matthiasnowak/jewelled/res/jewelled_chargerProgrammer_pcb_combined.png

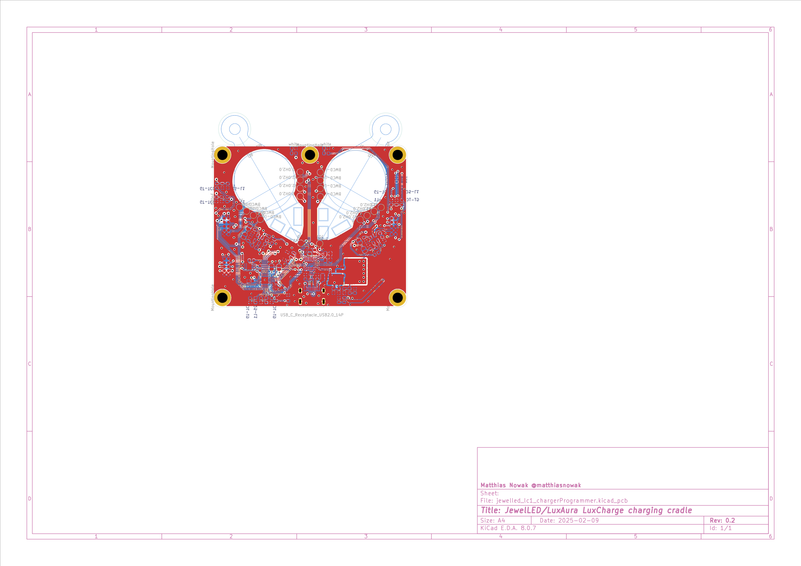
res/jewelled_chargerProgrammer_pcb_combined.png
