matthiasnowak/jewelled/res/jewelled_chargerProgrammer_render_back.png

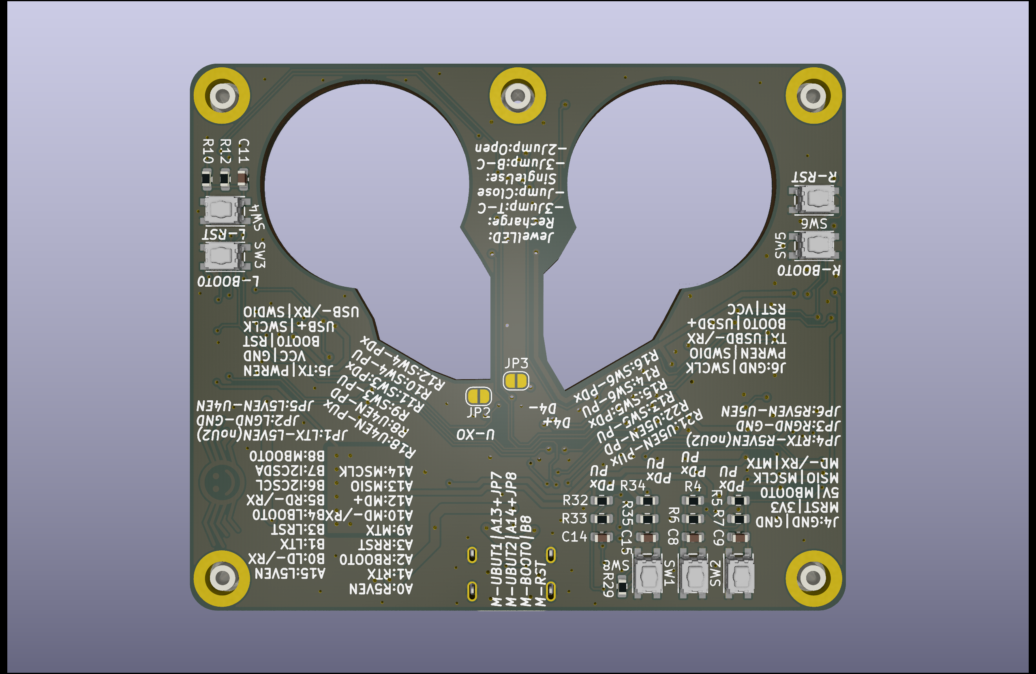
res/jewelled_chargerProgrammer_render_back.png
