matthiasnowak/jewelled/res/jewelled_dual_pcb_combined.png

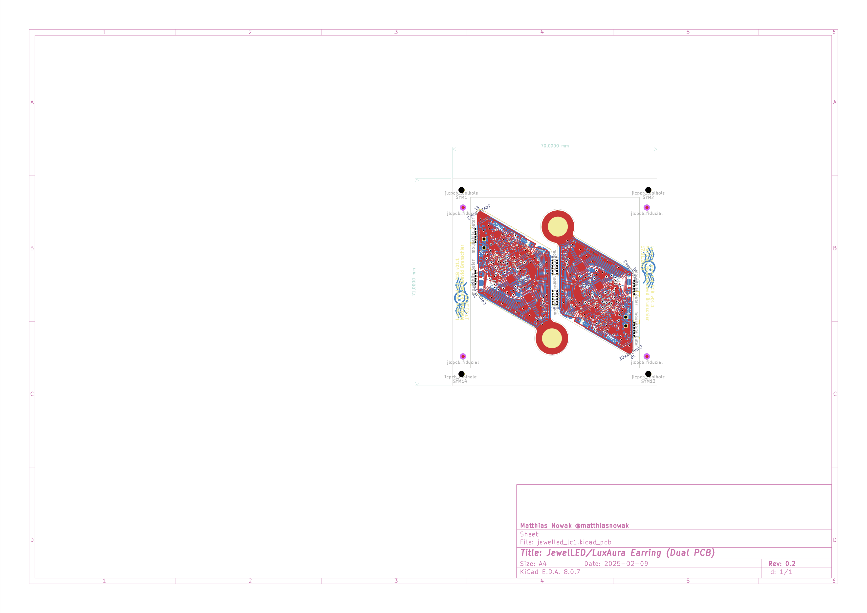
res/jewelled_dual_pcb_combined.png
