matthiasnowak/jewelled/software/CH32V203G6U6_jewelled_march/User/jewel_gpio.c

/*
 * jewel_gpio.c
 *
 *  Created on: 3 Mar 2025
 *      Author: matth
 */

#include "jewel_gpio.h"

void GPIO_Init_Config(void) {
    RCC_APB2PeriphClockCmd(RCC_APB2Periph_GPIOA, ENABLE);
    RCC_APB2PeriphClockCmd(RCC_APB2Periph_GPIOB, ENABLE);
    GPIO_InitTypeDef GPIO_InitStructure = {0};

    // GPIOB_0:     OPA1_P
    GPIO_InitStructure.GPIO_Pin = IO_OPA_P_PIN;
    GPIO_InitStructure.GPIO_Mode = GPIO_Mode_IN_FLOATING;
    GPIO_InitStructure.GPIO_Speed = GPIO_Speed_10MHz;
    GPIO_Init(IO_OPA_P_PORT, &GPIO_InitStructure);

    // GPIOA_6:     OPA1_N
    GPIO_InitStructure.GPIO_Pin = IO_OPA_N_PIN;
    GPIO_InitStructure.GPIO_Mode = GPIO_Mode_IN_FLOATING;
    GPIO_InitStructure.GPIO_Speed = GPIO_Speed_10MHz;
    GPIO_Init(IO_OPA_N_PORT, &GPIO_InitStructure);

    // GPIOB_1:     Dont init OPA1_OUT1 as GPIO
//    GPIO_InitStructure.GPIO_Pin = IO_OPA_O_PIN;
//    GPIO_InitStructure.GPIO_Mode = GPIO_Mode_AIN;
//    GPIO_InitStructure.GPIO_Speed = GPIO_Speed_10MHz;
//    GPIO_Init(IO_OPA_O_PORT, &GPIO_InitStructure);

    // GPIOA_5:     MICOUT
    GPIO_InitStructure.GPIO_Pin = IO_MICOUT_PIN;
    GPIO_InitStructure.GPIO_Mode = GPIO_Mode_AIN;
    GPIO_InitStructure.GPIO_Speed = GPIO_Speed_10MHz;
    GPIO_Init(IO_MICOUT_PORT, &GPIO_InitStructure);

    // GPIOA_0:     BUT1
    GPIO_InitStructure.GPIO_Pin = GPIO_Pin_0;
    GPIO_InitStructure.GPIO_Mode = GPIO_Mode_IPU;
    GPIO_InitStructure.GPIO_Speed = GPIO_Speed_50MHz;
    GPIO_Init(GPIOA, &GPIO_InitStructure);

    // GPIOA_1:     BUT2
    GPIO_InitStructure.GPIO_Pin = GPIO_Pin_1;
    GPIO_InitStructure.GPIO_Mode = GPIO_Mode_IPU;
    GPIO_InitStructure.GPIO_Speed = GPIO_Speed_50MHz;
    GPIO_Init(IO_BUT2_PORT, &GPIO_InitStructure);

    // GPIOA_2:     BUZZER
    GPIO_StructInit(&GPIO_InitStructure);
    GPIO_InitStructure.GPIO_Pin = IO_BUZZ_PIN;
    GPIO_InitStructure.GPIO_Mode = GPIO_Mode_Out_PP;
    GPIO_InitStructure.GPIO_Speed = GPIO_Speed_10MHz;
    GPIO_Init(IO_BUZZ_PORT, &GPIO_InitStructure);

    //    // GPIOA_4:     PERI_EN
    GPIO_WriteBit(IO_PERI_PORT, IO_PERI_PIN, Bit_SET); // Peripheral off
    GPIO_InitStructure.GPIO_Pin = IO_PERI_PIN;
    GPIO_InitStructure.GPIO_Mode = GPIO_Mode_Out_OD;
    GPIO_InitStructure.GPIO_Speed = GPIO_Speed_10MHz;
    GPIO_Init(IO_PERI_PORT, &GPIO_InitStructure);

    // GPIOA_3:     BATSENSE
    GPIO_StructInit(&GPIO_InitStructure);
    GPIO_InitStructure.GPIO_Pin = IO_BAT_PIN;
    GPIO_InitStructure.GPIO_Mode = GPIO_Mode_AIN;
    GPIO_InitStructure.GPIO_Speed = GPIO_Speed_10MHz;
    GPIO_Init(IO_BAT_PORT, &GPIO_InitStructure);

    // GPIOB_3:     CHARGESTATE
    GPIO_StructInit(&GPIO_InitStructure);
    GPIO_InitStructure.GPIO_Pin = IO_CHARGE_PIN;
    GPIO_InitStructure.GPIO_Mode = GPIO_Mode_IPU;
    GPIO_InitStructure.GPIO_Speed = GPIO_Speed_10MHz;
    GPIO_Init(IO_CHARGE_PORT, &GPIO_InitStructure);

    // GPIOB_8:     BOOT0
    GPIO_StructInit(&GPIO_InitStructure);
    GPIO_InitStructure.GPIO_Pin = IO_BOOT0_PIN;
    GPIO_InitStructure.GPIO_Mode = GPIO_Mode_IN_FLOATING;
    GPIO_InitStructure.GPIO_Speed = GPIO_Speed_10MHz;
    GPIO_Init(IO_BOOT0_PORT, &GPIO_InitStructure);

    // GPIOB_6:     SCL
    GPIO_StructInit(&GPIO_InitStructure);
    GPIO_InitStructure.GPIO_Pin = IO_SCL_PIN;
    GPIO_InitStructure.GPIO_Mode = GPIO_Mode_AF_OD;
    GPIO_InitStructure.GPIO_Speed = GPIO_Speed_50MHz;
    GPIO_Init(IO_SCL_PORT, &GPIO_InitStructure);

    // GPIOB_7:     SDA
    GPIO_StructInit(&GPIO_InitStructure);
    GPIO_InitStructure.GPIO_Pin = IO_SDA_PIN;
    GPIO_InitStructure.GPIO_Mode = GPIO_Mode_AF_OD;
    GPIO_InitStructure.GPIO_Speed = GPIO_Speed_50MHz;
    GPIO_Init(IO_SDA_PORT, &GPIO_InitStructure);

    // GPIOB_7:     SDB
    GPIO_StructInit(&GPIO_InitStructure);
    GPIO_InitStructure.GPIO_Pin = IO_LED_SDB_PIN;
    GPIO_InitStructure.GPIO_Mode = GPIO_Mode_Out_PP;
    GPIO_InitStructure.GPIO_Speed = GPIO_Speed_10MHz;
    GPIO_Init(IO_LED_SDB_PORT, &GPIO_InitStructure);

    // GPIOA_9:     TX
    GPIO_StructInit(&GPIO_InitStructure);
    GPIO_InitStructure.GPIO_Pin = GPIO_Pin_9;
    GPIO_InitStructure.GPIO_Mode = GPIO_Mode_AF_PP;
    //GPIO_InitStructure.GPIO_Mode = GPIO_Mode_IN_FLOATING;
    GPIO_InitStructure.GPIO_Speed = GPIO_Speed_50MHz;
    GPIO_Init(GPIOA, &GPIO_InitStructure);

    // GPIOA_10:     RX
    GPIO_StructInit(&GPIO_InitStructure);
    GPIO_InitStructure.GPIO_Pin = GPIO_Pin_10;
    GPIO_InitStructure.GPIO_Mode = GPIO_Mode_IN_FLOATING;
    GPIO_InitStructure.GPIO_Speed = GPIO_Speed_50MHz;
    GPIO_Init(GPIOA, &GPIO_InitStructure);

    GPIO_StructInit(&GPIO_InitStructure);
    GPIO_InitStructure.GPIO_Pin = GPIO_Pin_13;
    GPIO_InitStructure.GPIO_Mode = GPIO_Mode_IN_FLOATING;
    GPIO_InitStructure.GPIO_Speed = GPIO_Speed_50MHz;
    GPIO_Init(GPIOA, &GPIO_InitStructure);

    GPIO_StructInit(&GPIO_InitStructure);
    GPIO_InitStructure.GPIO_Pin = GPIO_Pin_12;
    GPIO_InitStructure.GPIO_Mode = GPIO_Mode_IN_FLOATING;
    GPIO_InitStructure.GPIO_Speed = GPIO_Speed_50MHz;
    GPIO_Init(GPIOA, &GPIO_InitStructure);

    GPIO_StructInit(&GPIO_InitStructure);
    GPIO_InitStructure.GPIO_Pin = GPIO_Pin_11;
    GPIO_InitStructure.GPIO_Mode = GPIO_Mode_IN_FLOATING;
    GPIO_InitStructure.GPIO_Speed = GPIO_Speed_50MHz;
    GPIO_Init(GPIOA, &GPIO_InitStructure);

    GPIO_StructInit(&GPIO_InitStructure);
    GPIO_InitStructure.GPIO_Pin = GPIO_Pin_14;
    GPIO_InitStructure.GPIO_Mode = GPIO_Mode_IN_FLOATING;
    GPIO_InitStructure.GPIO_Speed = GPIO_Speed_50MHz;
    GPIO_Init(GPIOA, &GPIO_InitStructure);

    GPIO_StructInit(&GPIO_InitStructure);
    GPIO_InitStructure.GPIO_Pin = GPIO_Pin_8;
    GPIO_InitStructure.GPIO_Mode = GPIO_Mode_IN_FLOATING;
    GPIO_InitStructure.GPIO_Speed = GPIO_Speed_50MHz;
    GPIO_Init(GPIOB, &GPIO_InitStructure);
}

void GPIO_Peripheral_Wakeup(void) {
    GPIO_WriteBit(IO_PERI_PORT, IO_PERI_PIN, Bit_RESET);
}

void GPIO_Peripheral_Sleep(void) {
    GPIO_WriteBit(IO_PERI_PORT, IO_PERI_PIN, Bit_SET);
}
