matthiasnowak/jewelled/software/CH32V203G6U6_jewelled_march/User/jewel_adc.h

/*
 * jewel_adc.h
 *
 *  Created on: 3 Mar 2025
 *      Author: matth
 */

#ifndef USER_JEWEL_ADC_H_
#define USER_JEWEL_ADC_H_

#include "ch32v20x.h"
#include "ch32v20x_conf.h"
#include "ch32v20x_opa.h"
#include "jewel_config.h"

void ADC_Init_Config(void);

#endif /* USER_JEWEL_ADC_H_ */
