matthiasnowak/jewelled/software/CH32V203G6U6_jewelledprogrammer_test1/User/leddriver.c

#include "LedDriver.h"
#include <stdio.h> // For example output

// Initializes the LED driver
//void LedDriver_Init(LedDriver* driver, int pin) {
//    driver->pin = pin;
//    driver->init = LedDriver_Init;
//    driver->turnOn = LedDriver_TurnOn;
//    driver->turnOff = LedDriver_TurnOff;
//
//    // Initialize the pin (e.g., configure as output)
//    printf("LED Driver initialized on pin %d\n", pin);
//}
//
//// Turns on the LED
//void LedDriver_TurnOn(int pin) {
//    // Code to turn on the LED at the specified pin
//    printf("LED on pin %d is turned ON\n", pin);
//}
//
//// Turns off the LED
//void LedDriver_TurnOff(int pin) {
//    // Code to turn off the LED at the specified pin
//    printf("LED on pin %d is turned OFF\n", pin);
//}



void LedDriver_Init(LedDriver* driver) {

}

void LedDriver_WriteData(LedDriver* driver, u8* data, u8 length) {

}

void LedDriver_WriteGlobalData(LedDriver* driver, u8 data) {

}

void LedDriver_Update(LedDriver* driver) {

}

void LedDriver_SetSoftwareShutdown(LedDriver* driver, LedDriverSSD_Typedef valSSD) {

}

void LedDriver_SetCurrent(LedDriver* driver, LedDriverCurrent_Typedef* data, u8 length) {

}

void LedDriver_SetGlobalCurrent(LedDriver* driver, LedDriverCurrent_Typedef valCurr) {

}

void LedDriver_SetGlobalControl(LedDriver* driver, LedDriverGC_Typedef valGC) {

}

void LedDriver_SetFrequency(LedDriver* driver, LedDriverFreq_Typedef valFreq) {

}

void LedDriver_SetGammeTable(LedDriver* driver, LedDriverGammaTable_Typedef valGamma) {

}

void LedDriver_Reset(LedDriver* driver) {

}
