matthiasnowak/jewelled/software/CH32V203G6U6_jewelled_march/User/jewel_ui.h

/*
 * jewel_ui.h
 *
 *  Created on: 9 Mar 2025
 *      Author: matth
 */

#ifndef USER_JEWEL_UI_H_
#define USER_JEWEL_UI_H_

#include "ch32v20x.h"
#include "ch32v20x_conf.h"
#include "jewel_config.h"
//#include "math.h"



void UI_Init(void);

#endif /* USER_JEWEL_UI_H_ */
